oskar2517/vfd-tube-calculator/assets/finished_1.jpg

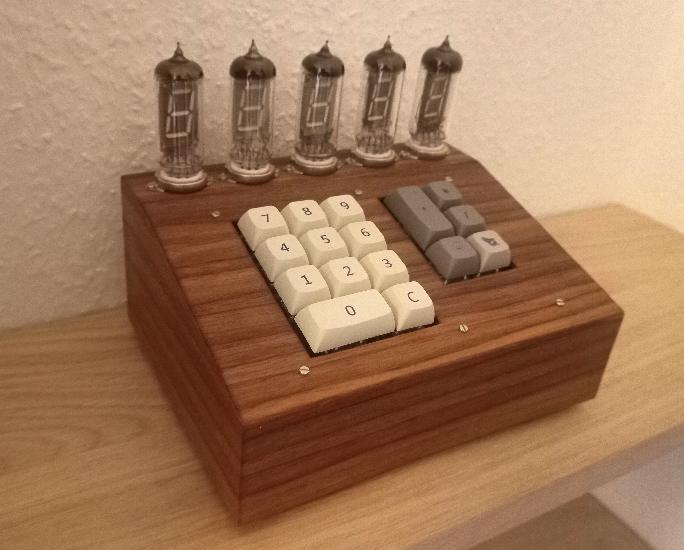
assets/finished_1.jpg
