oskar2517/vfd-tube-calculator/assets/finished_2.jpg

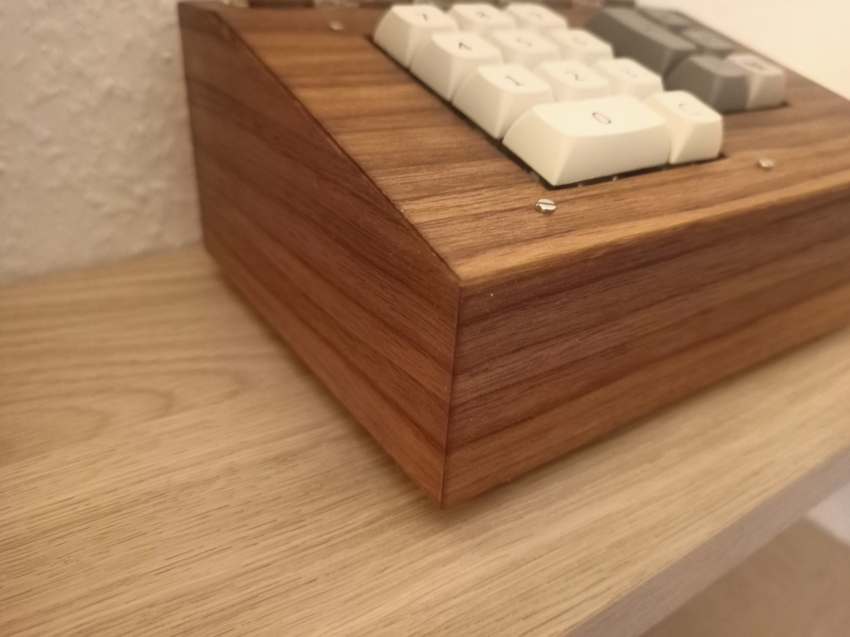
assets/finished_2.jpg
