oskar2517/vfd-tube-calculator/assets/finished_3.jpg

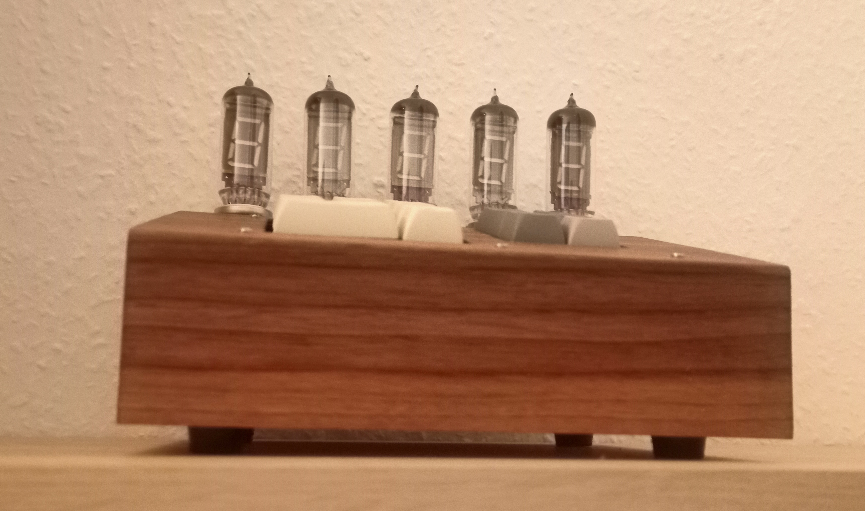
assets/finished_3.jpg
