oskar2517/vfd-tube-calculator/assets/finished_4.jpg

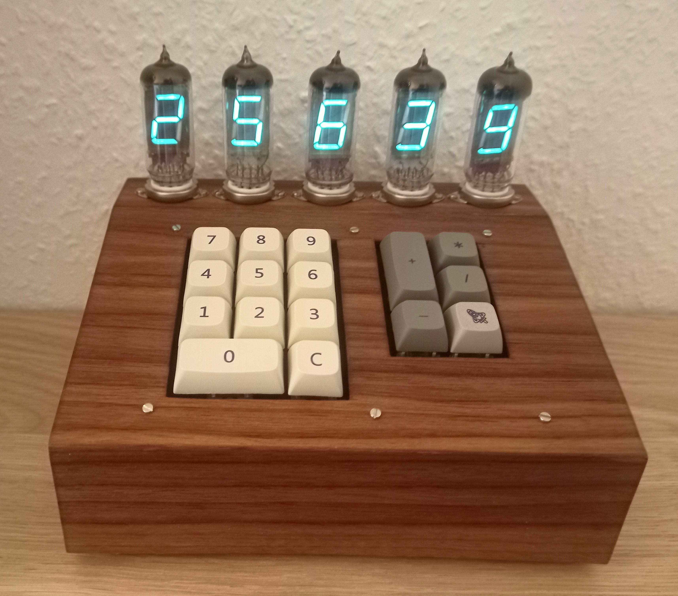
assets/finished_4.jpg
